le0m/led-matrix/src/modules/config.h

#ifndef _CONFIG_H
#define _CONFIG_H

#include "../modules/log.h"
#include "filesystem.h"
#include <ArduinoJson.h>
#include <ESPAsyncWebServer.h>
#include <AsyncJson.h>

typedef std::function<void(JsonDocument& cfg)> ConfigChangeHandler;

class Config {
    private:
        JsonDocument newCfg;
        ConfigChangeHandler configChangeHandler;
        static void merge(JsonVariant, JsonVariantConst);
        static void asyncUpdateConfig(void*);

    public:
        JsonDocument current;
        Config(ConfigChangeHandler);
        ~Config();
        void initServer(AsyncWebServer*);
        bool save(const char* = "/config.json");
        bool load(const char* = "/config.json");
};

#endif
